pfroud/DMX-controller/OAK A50K slide potentiometer info/Which pins are wiper and resistor.png

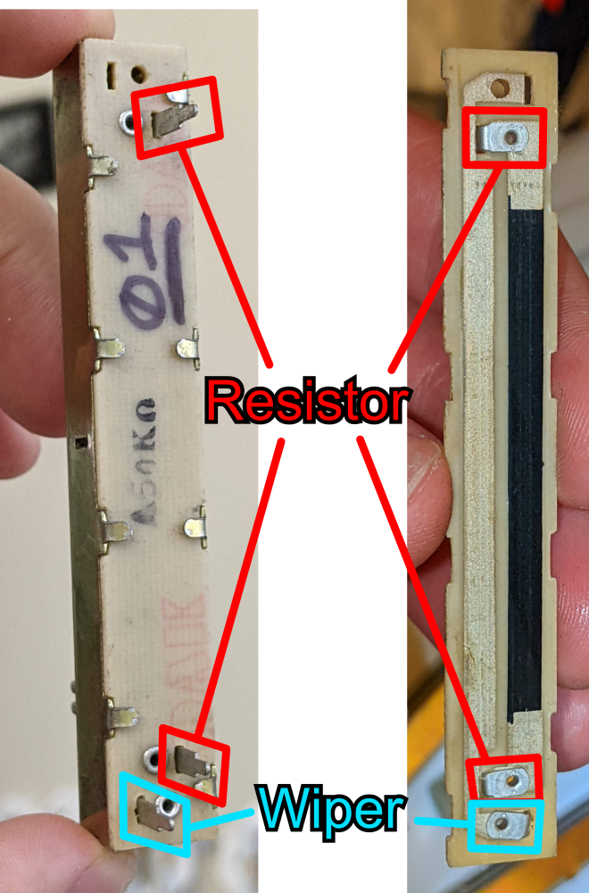
OAK A50K slide potentiometer info/Which pins are wiper and resistor.png
